MKme/Engine-Doctor/_ photos/Capture.JPG

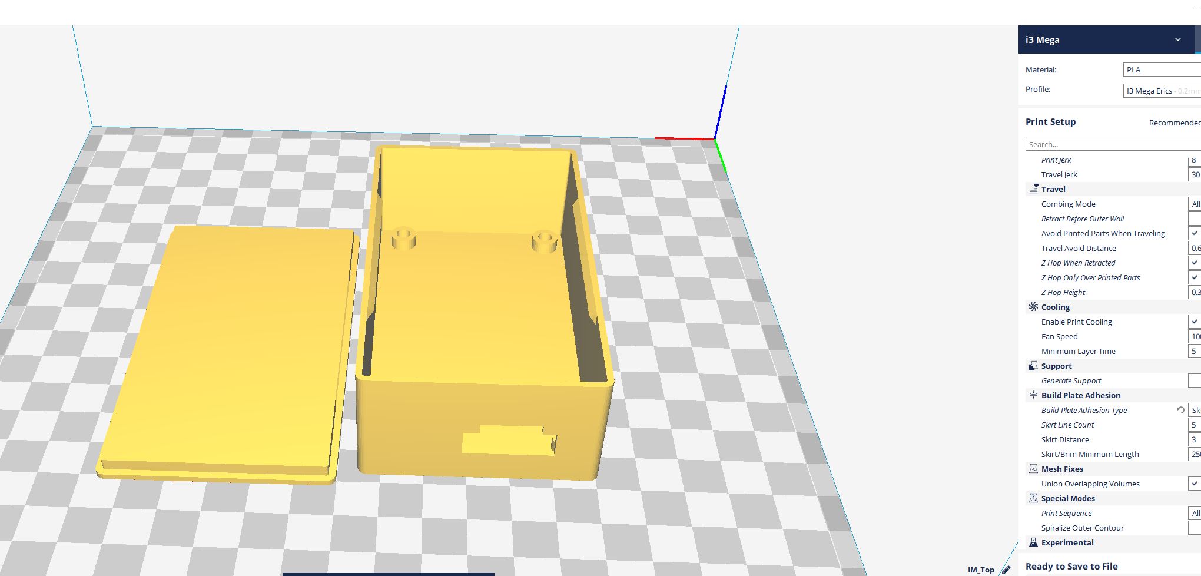
_ photos/Capture.JPG
