MKme/Engine-Doctor/_ photos/code working.PNG

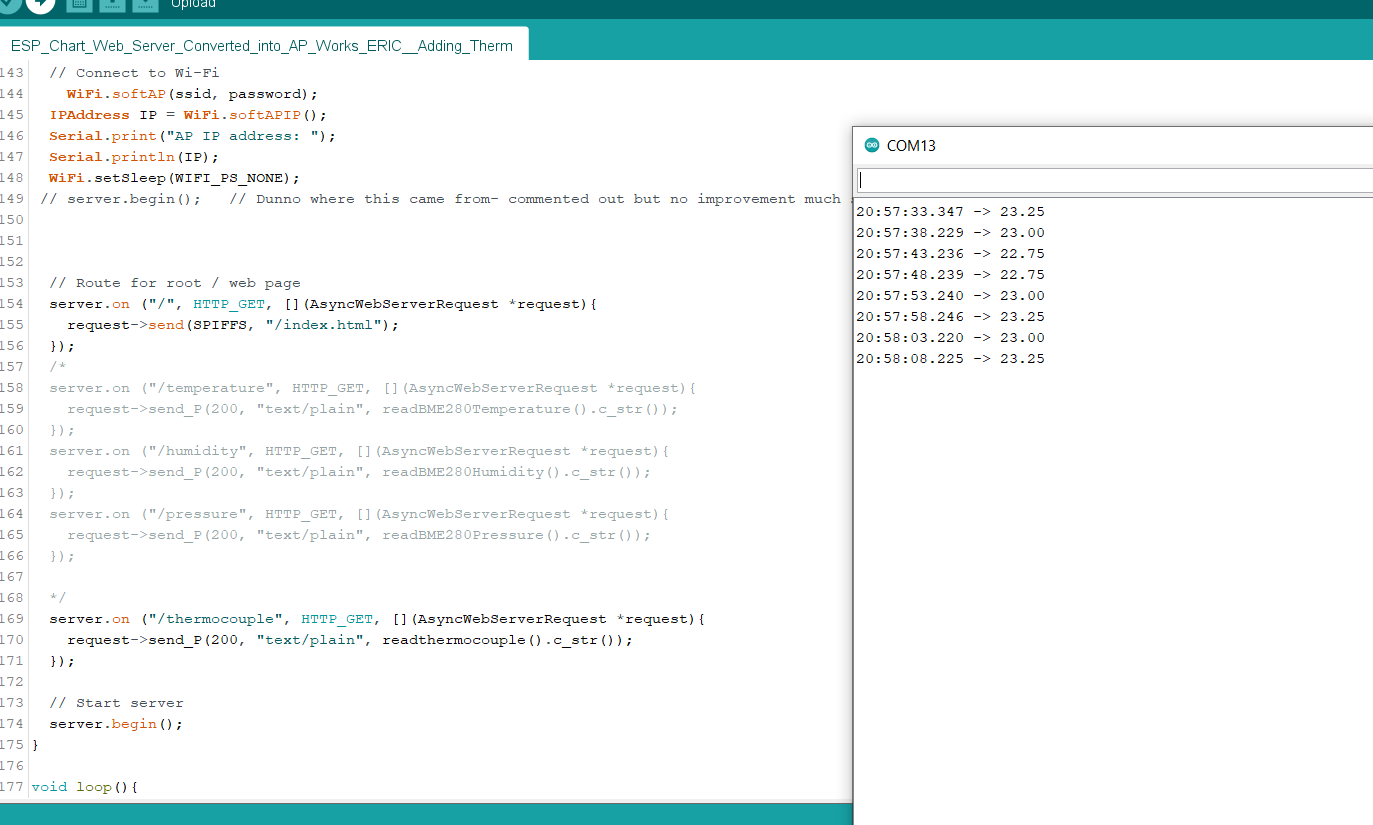
_ photos/code working.PNG
