MKme/Engine-Doctor/_ photos/DC009ED2-2DBB-4F93-A65B-17DDB9B75807.jpg

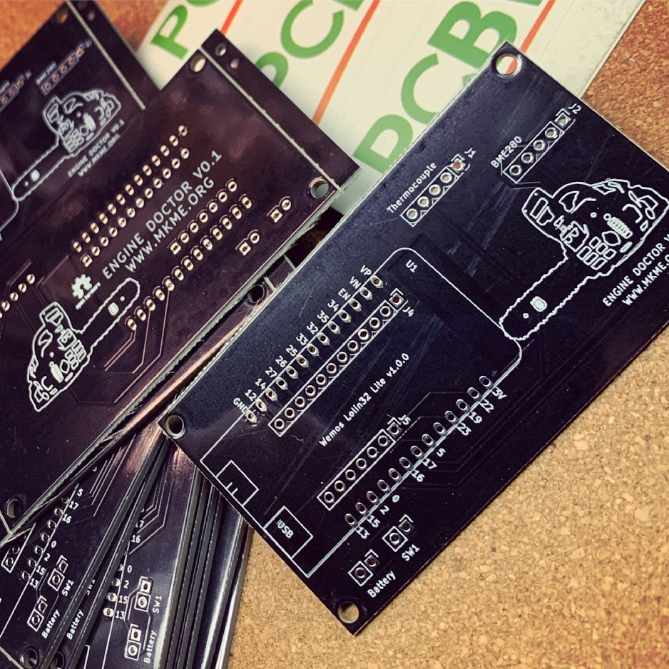
_ photos/DC009ED2-2DBB-4F93-A65B-17DDB9B75807.jpg
