MKme/Engine-Doctor/_ photos/EngieDoctor_Breadboard_Prototype.jpg

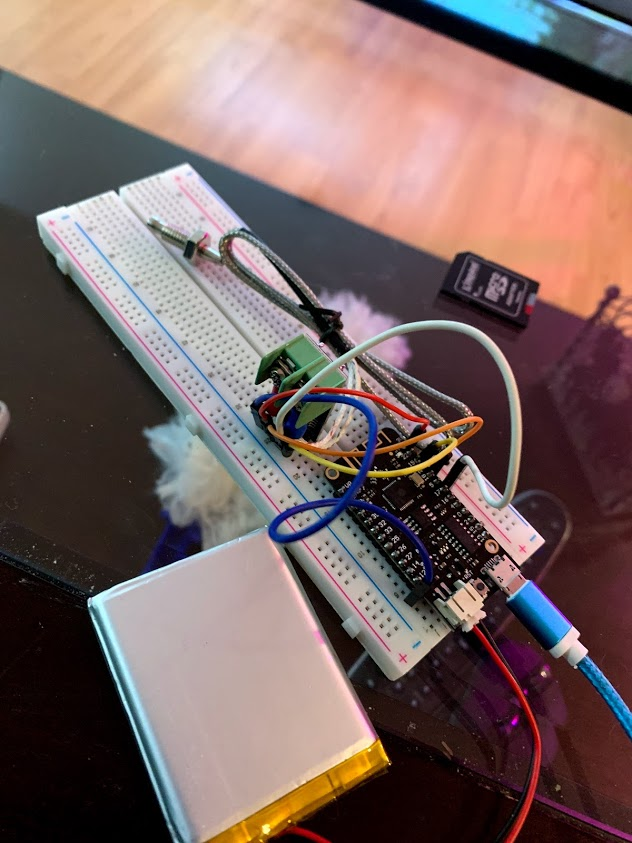
_ photos/EngieDoctor_Breadboard_Prototype.jpg
