MKme/Engine-Doctor/_ photos/IMG_2190.jpg

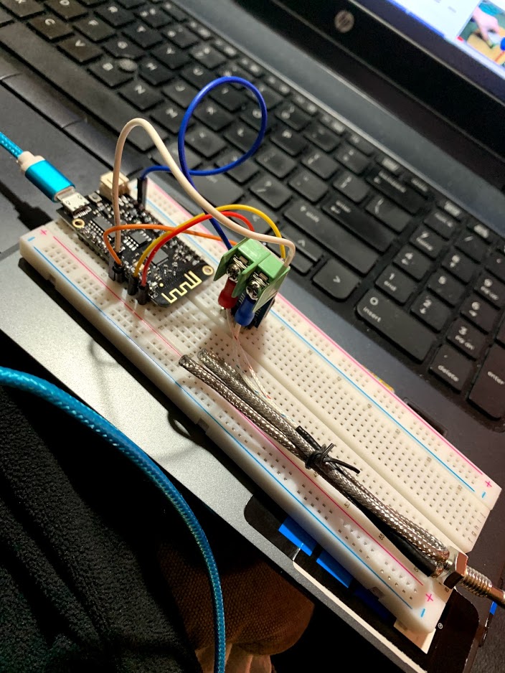
_ photos/IMG_2190.jpg
