MKme/Engine-Doctor/_ photos/IMG_2198.png

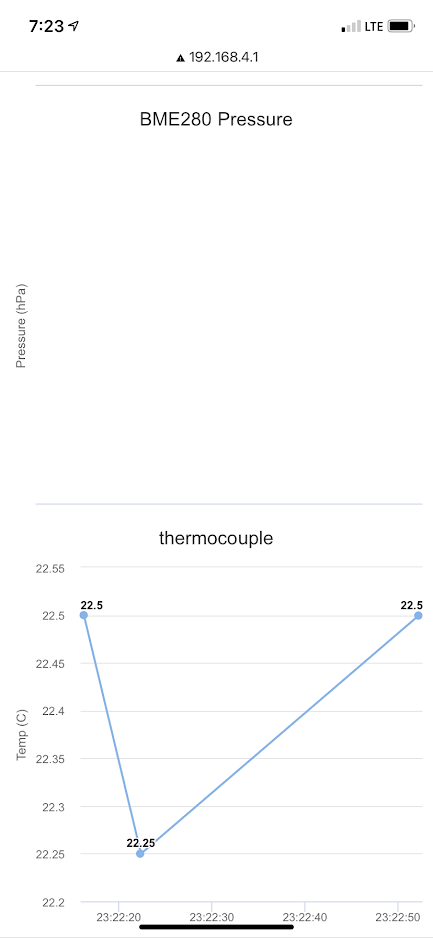
_ photos/IMG_2198.png
