MKme/Engine-Doctor/_ photos/IMG_2200.jpg

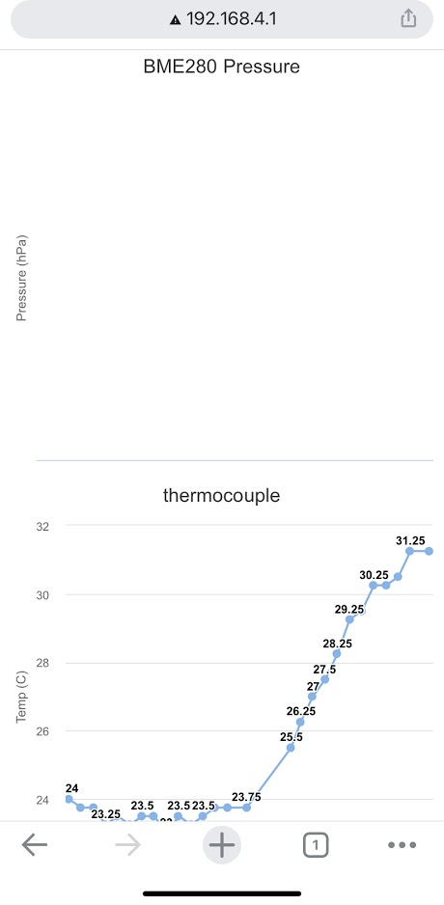
_ photos/IMG_2200.jpg
