MKme/Engine-Doctor/_ photos/IMG_2205LiveDataWorking.PNG

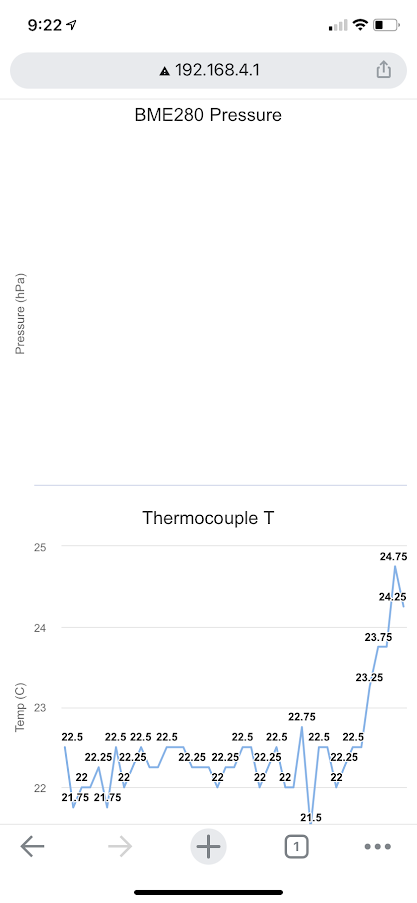
_ photos/IMG_2205LiveDataWorking.PNG
