MKme/Engine-Doctor/_ photos/IMG_2295.jpg

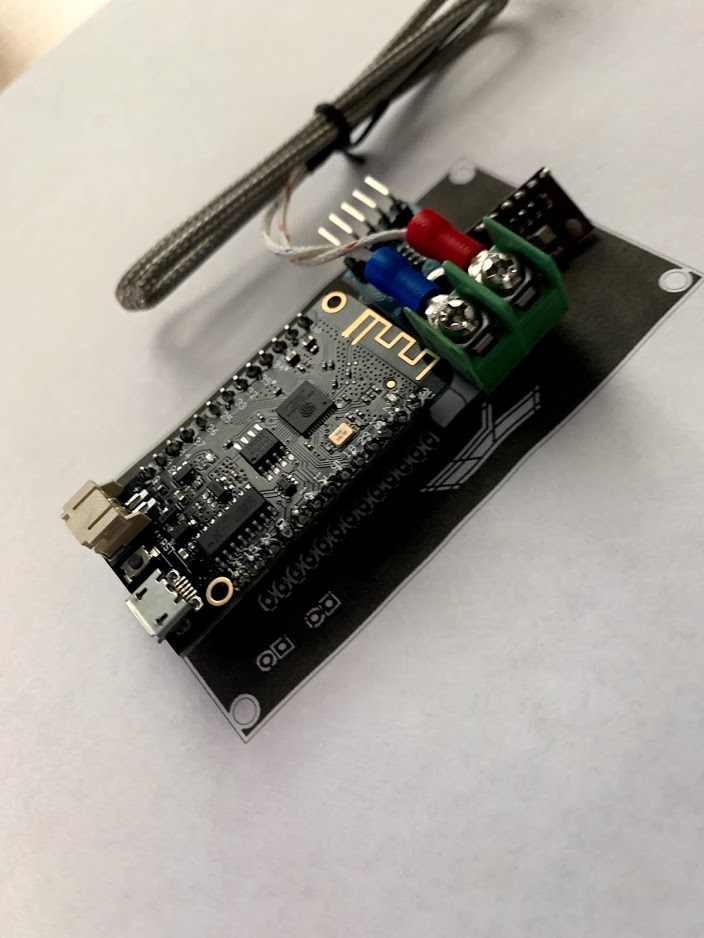
_ photos/IMG_2295.jpg
