MKme/Engine-Doctor/_ photos/IMG_2296.jpg

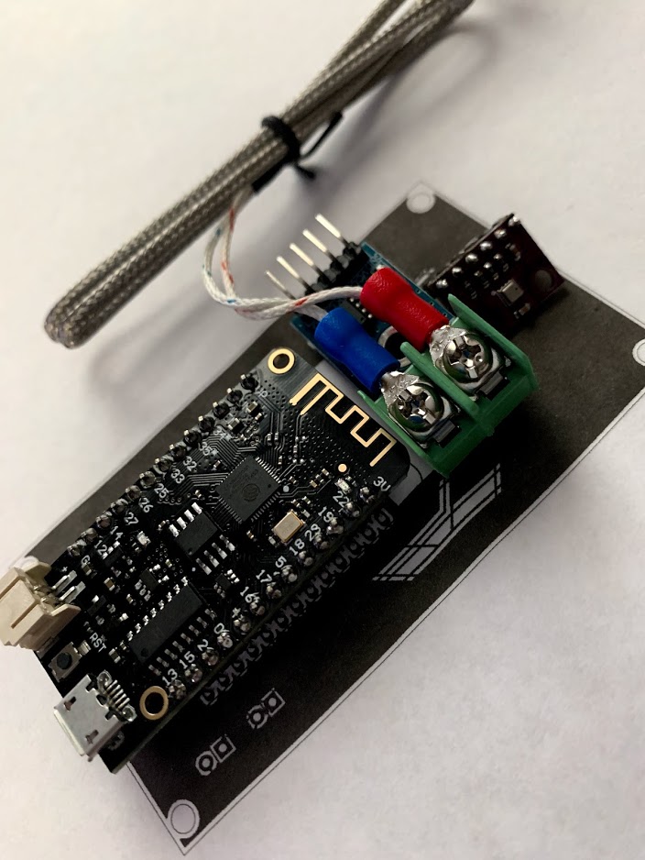
_ photos/IMG_2296.jpg
