MKme/Engine-Doctor/_ photos/IMG_2297.jpg

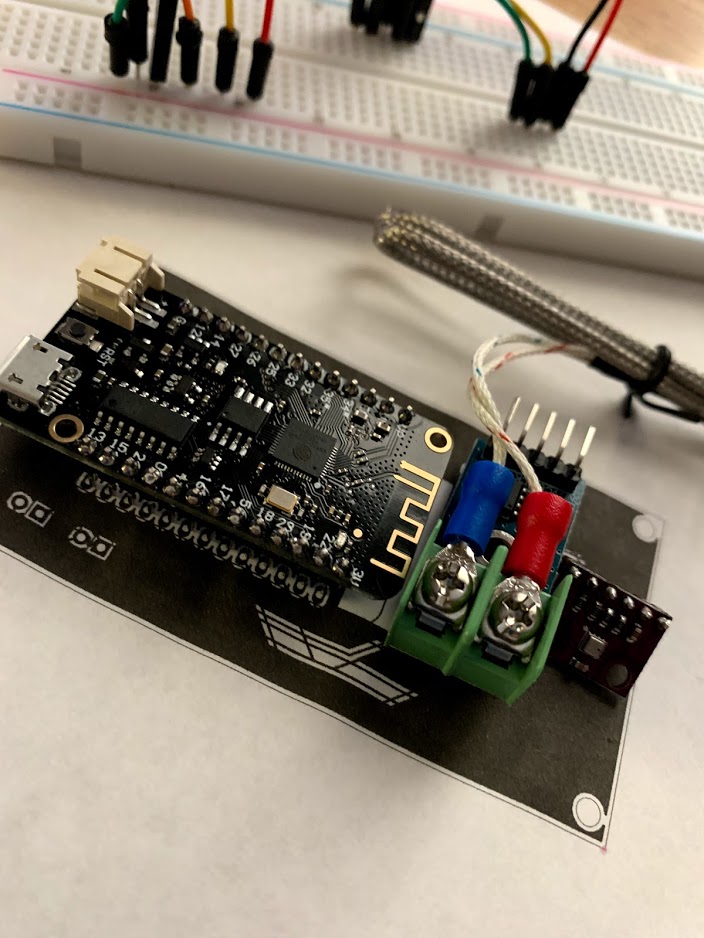
_ photos/IMG_2297.jpg
