MKme/Engine-Doctor/_ photos/IMG_2968.jpg

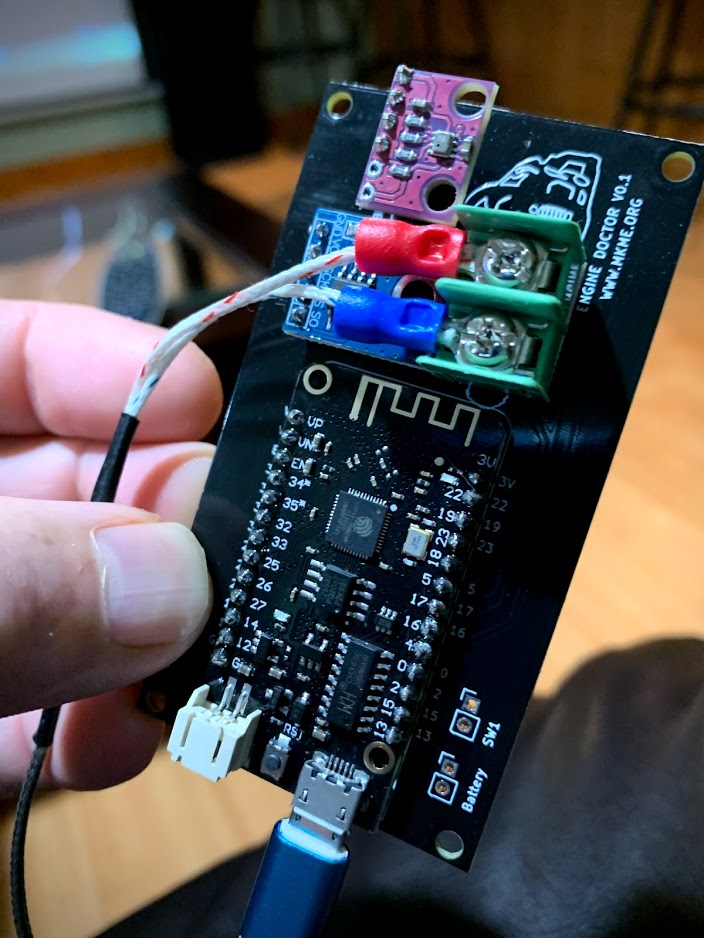
_ photos/IMG_2968.jpg
