MKme/Engine-Doctor/_ photos/IMG_3085.jpg

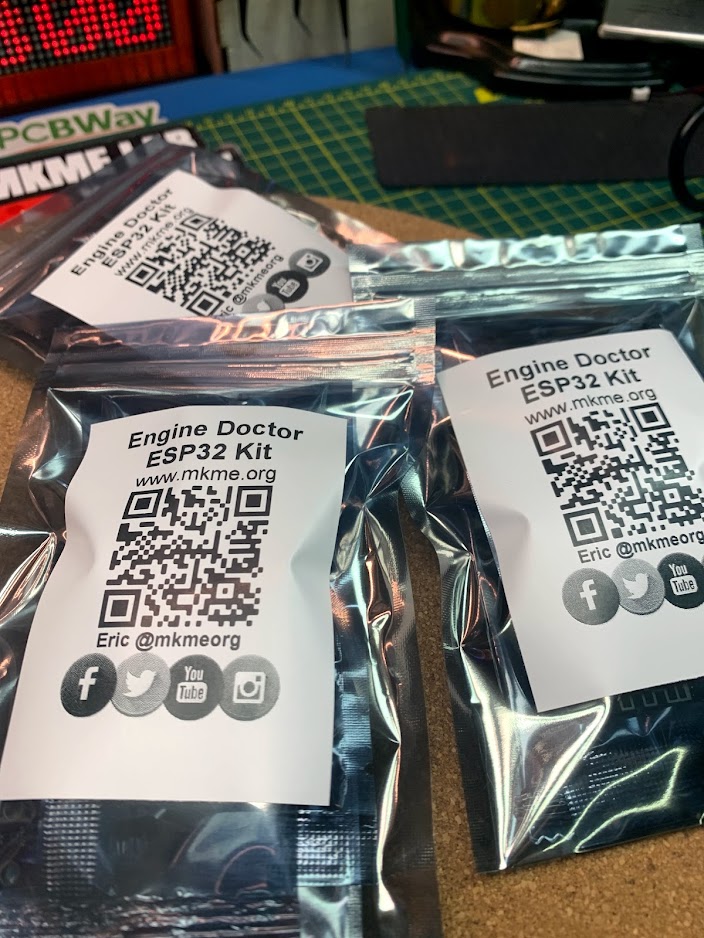
_ photos/IMG_3085.jpg
