MKme/Engine-Doctor/_ photos/IMG_3087.jpg

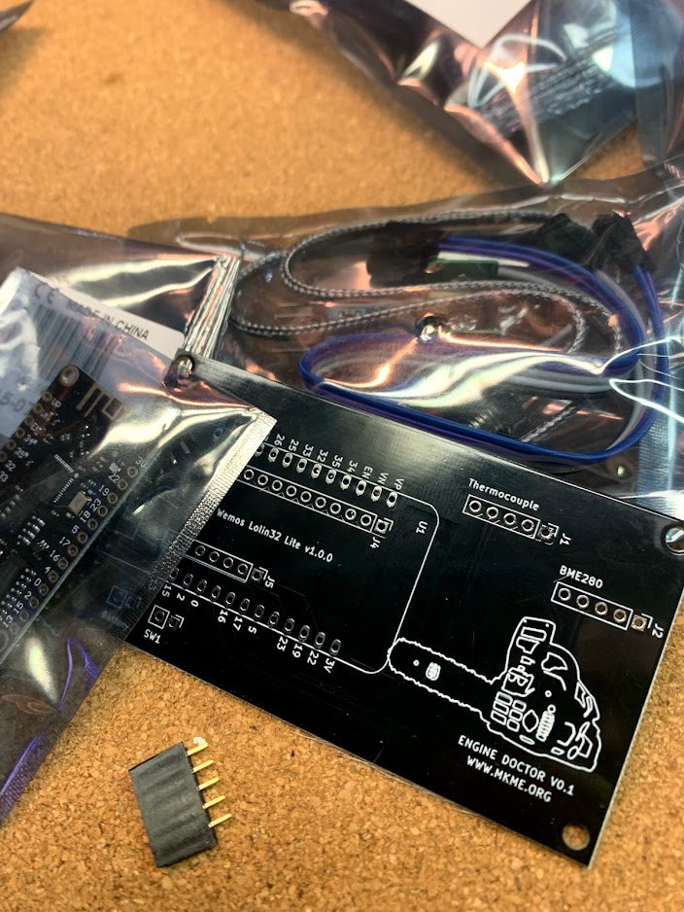
_ photos/IMG_3087.jpg
