MKme/Engine-Doctor/_ photos/IMG_3088.jpg

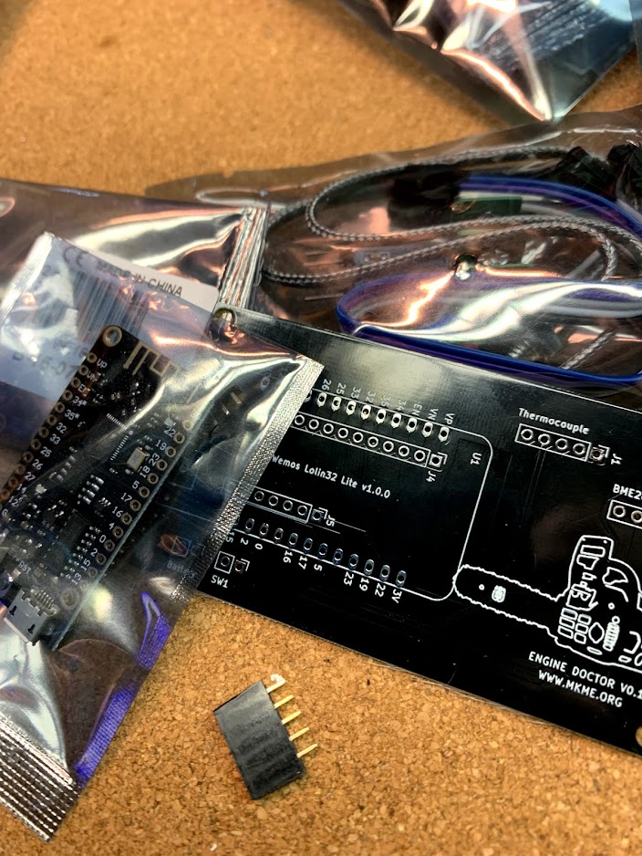
_ photos/IMG_3088.jpg
