MKme/Engine-Doctor/_ photos/IMG_3090.jpg

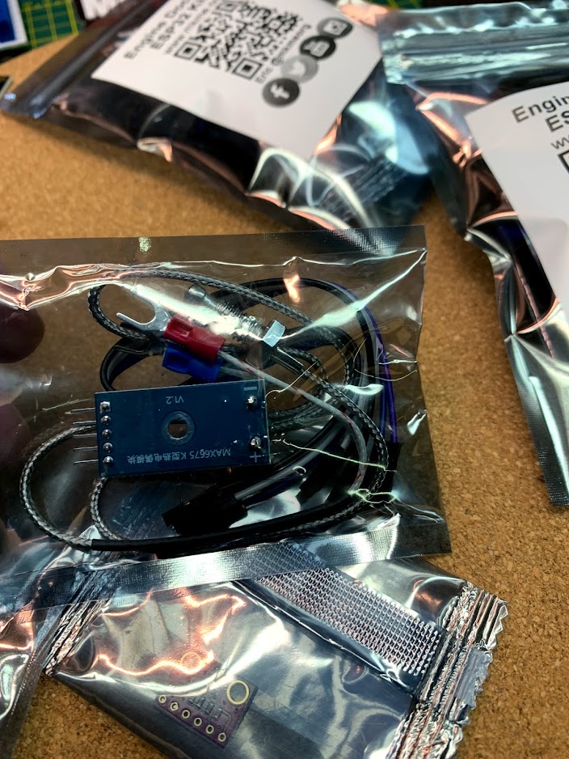
_ photos/IMG_3090.jpg
