MKme/Engine-Doctor/_ photos/IMG_3091.jpg

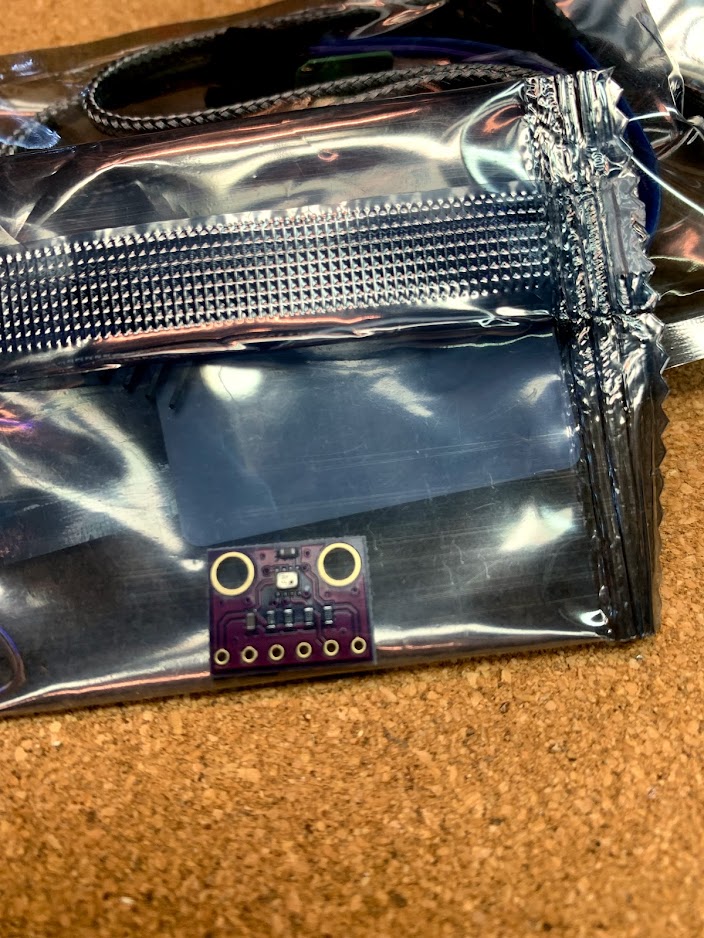
_ photos/IMG_3091.jpg
