MKme/Engine-Doctor/_ photos/IMG_3092.jpg

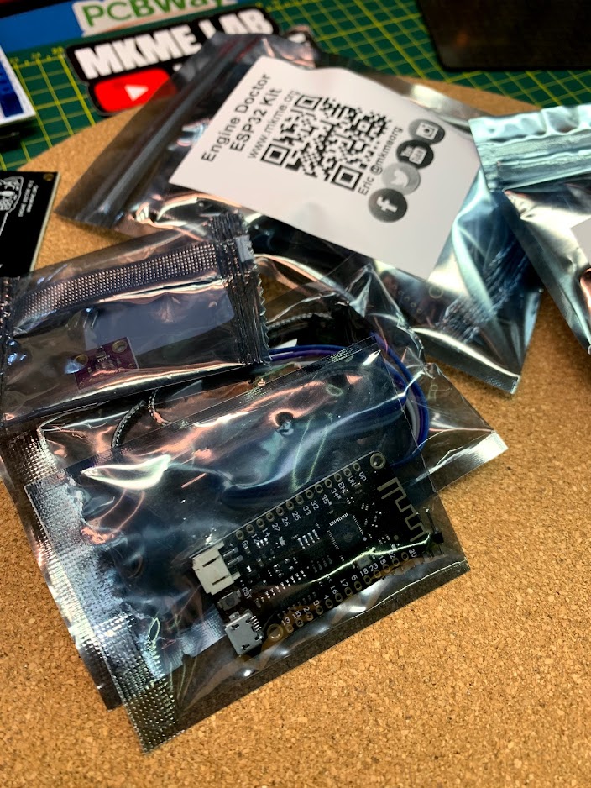
_ photos/IMG_3092.jpg
