MKme/Engine-Doctor/_ photos/IMG_3093.jpg

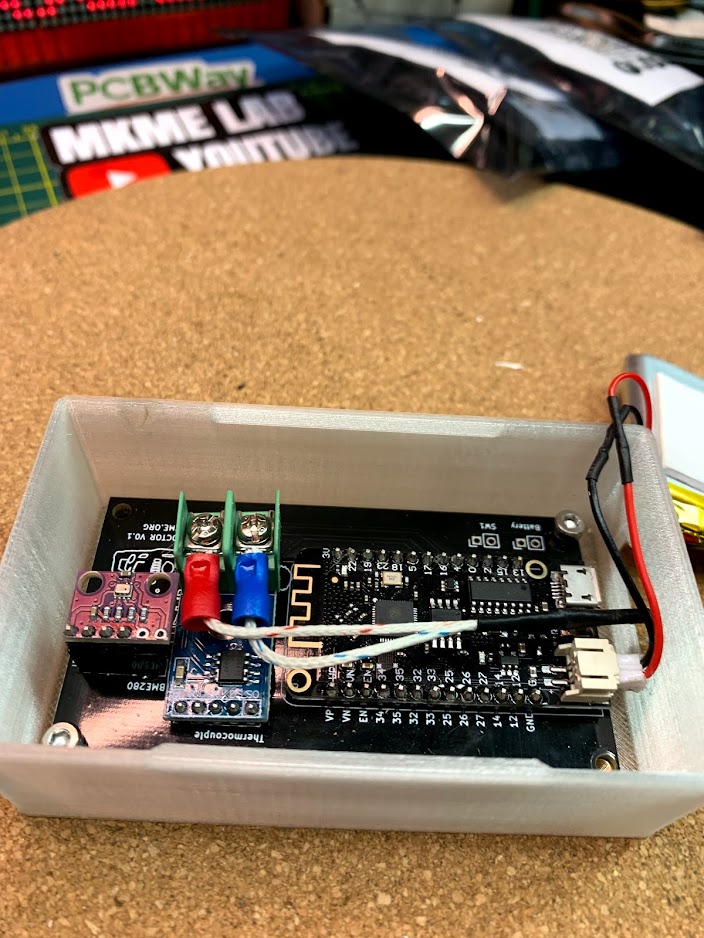
_ photos/IMG_3093.jpg
