MKme/Engine-Doctor/_ photos/IMG_3095.jpg

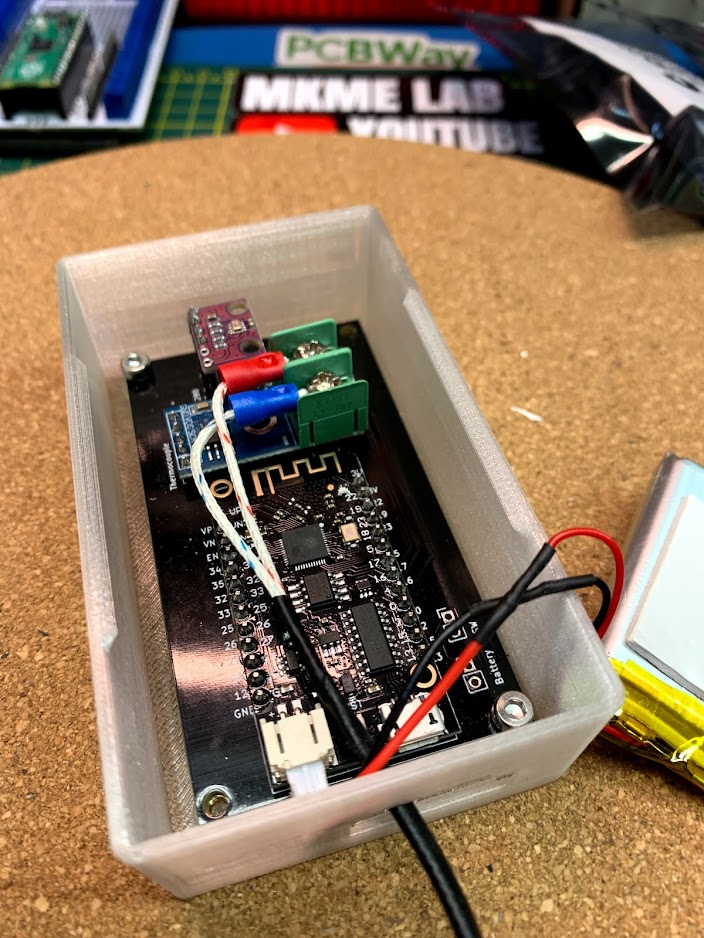
_ photos/IMG_3095.jpg
