MKme/Engine-Doctor/_ photos/IMG_3103.jpg

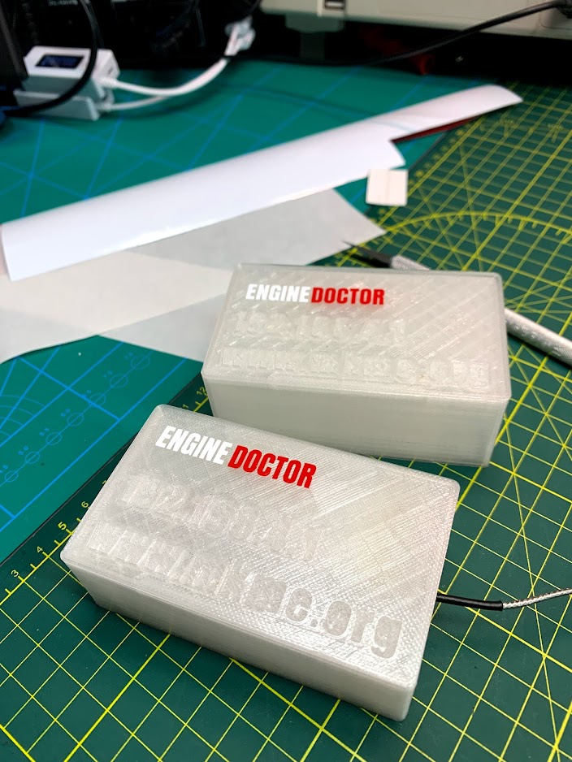
_ photos/IMG_3103.jpg
