MKme/Engine-Doctor/_ photos/IMG_3142.jpg

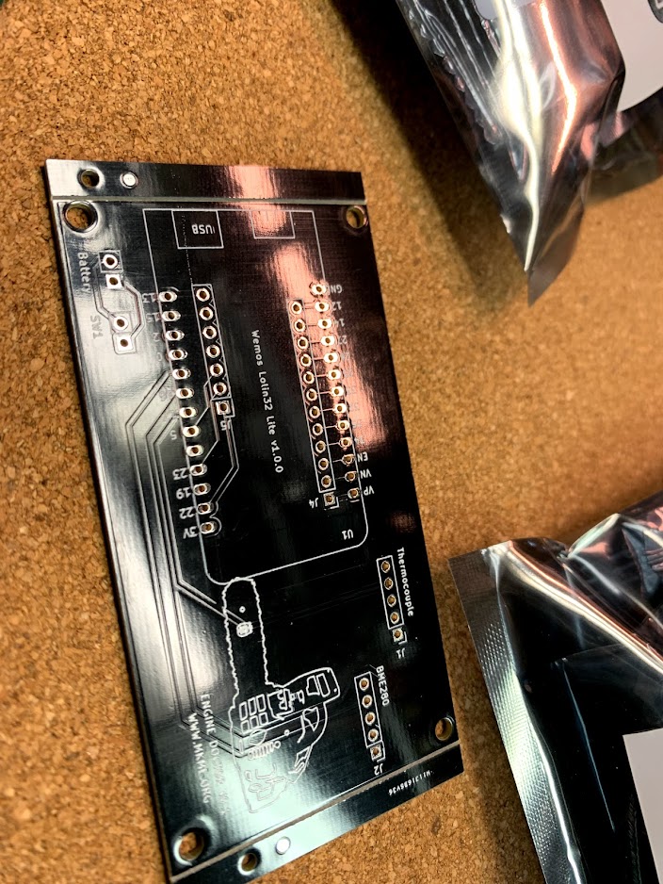
_ photos/IMG_3142.jpg
