MKme/Engine-Doctor/_ photos/IMG_3143.jpg

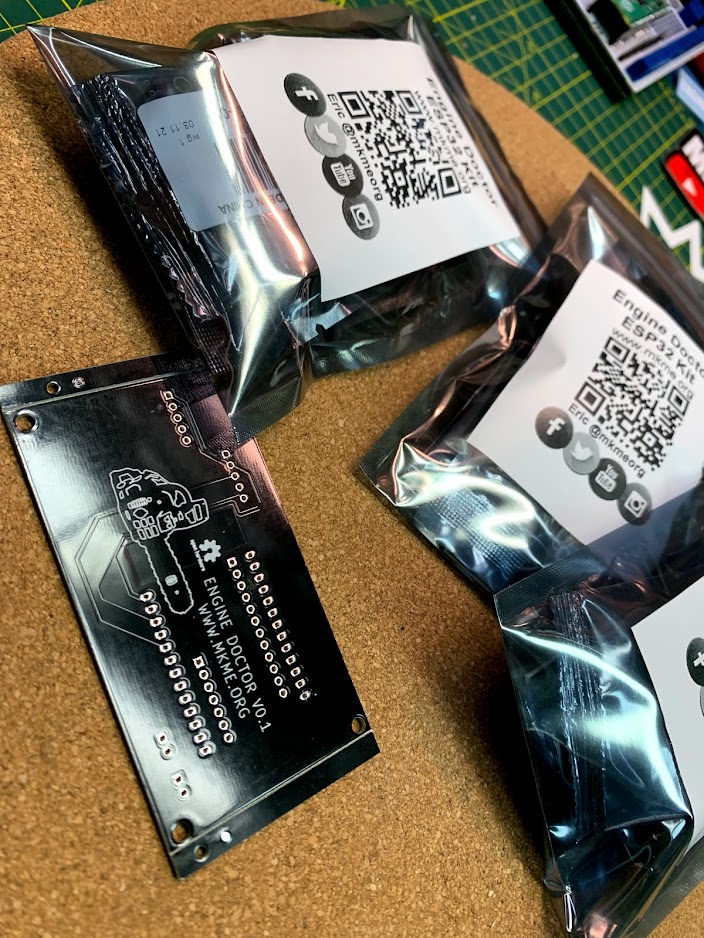
_ photos/IMG_3143.jpg
