MKme/Engine-Doctor/_ photos/IMG_3145.jpg

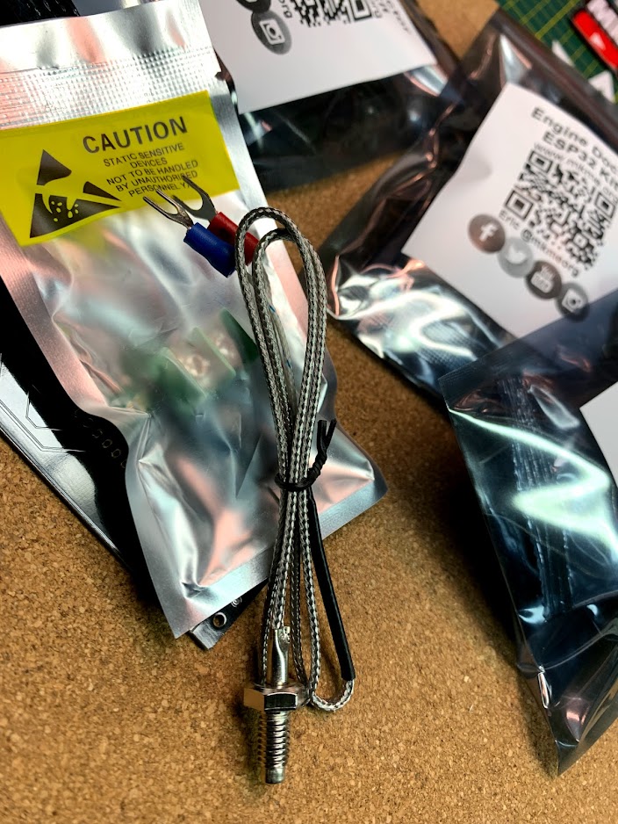
_ photos/IMG_3145.jpg
