MKme/Engine-Doctor/_ photos/IMG_3148.jpg

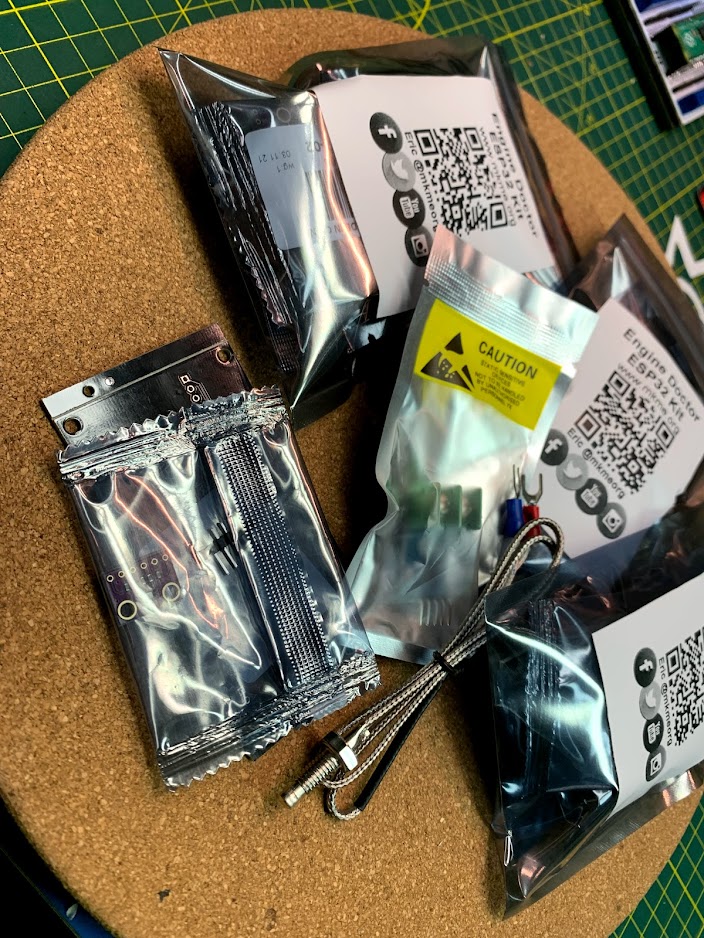
_ photos/IMG_3148.jpg
