MKme/Engine-Doctor/_ photos/vlcsnap-2021-05-02-12h10m35s916.png

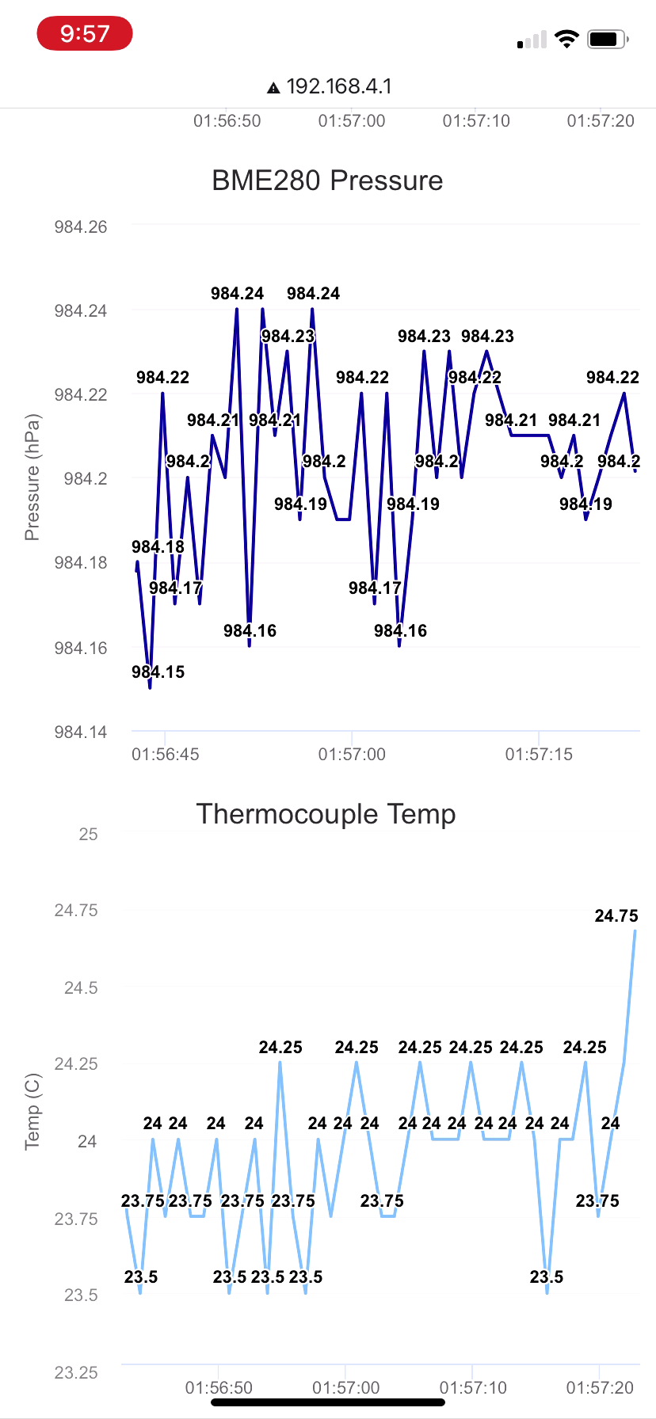
_ photos/vlcsnap-2021-05-02-12h10m35s916.png
